sotpotatis/pomodoro-timer/pcb/production_files/rev 1.0.1/pcbway/sample_pcbway_order_information.png

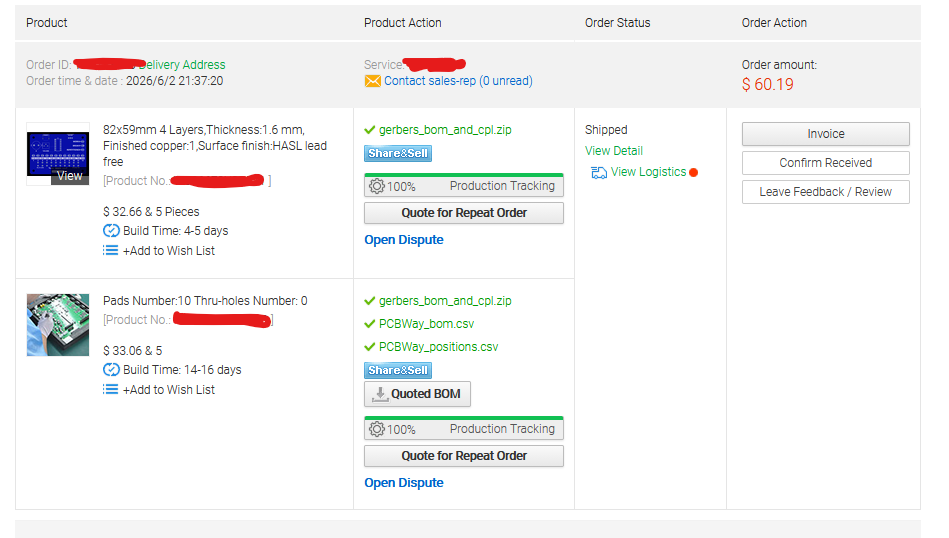
pcb/production_files/rev 1.0.1/pcbway/sample_pcbway_order_information.png
