sotpotatis/pomodoro-timer/tests/charlieplexing_15_pins/charlieplexing_15_pins/charlieplexing_15_pins.ino

/* charlieplexing_15_leds.ino
Test Arduino sketch (to run on an Arduino UNO, not Attinys)
for testing 5 pin Charlieplexing, which I added in the middle of my project.
Lights up each Charlieplexing LED at a time with a short delay in between
*/
// All GPIO pins in use.
const char TOTAL_PINS = 5;
 const char gpioPins[TOTAL_PINS] = {
   7,
   6,
   5,
   4,
   3
 };
// Contains the pins to set to output HIGH and output LOW to lit each of the 12 LEDs
// Led i is represented by index i in this map, and is in the format {pin to set to low, pin to set to high}
// Other pins are input pins.
// My schematic pins are called JP1, JP2, JP3, JP4, correspodning to GPIO pin number 1, 2, 3 and 4.
const char allPinStates[15][2] = {
  {gpioPins[1], gpioPins[0]}, // LED1  -> JP2 LOW, JP1 HIGH
  {gpioPins[0], gpioPins[1]}, // LED2  -> JP1 LOW, JP2 HIGH
  {gpioPins[2], gpioPins[0]}, // LED3  -> JP3 LOW, JP1 HIGH
  {gpioPins[0], gpioPins[2]}, // LED4  -> JP1 LOW, JP3 HIGH
  {gpioPins[3], gpioPins[0]}, // LED5  -> JP4 LOW, JP1 HIGH
  {gpioPins[0], gpioPins[3]}, // LED6  -> JP1 LOW, JP4 HIGH
  {gpioPins[2], gpioPins[1]}, // LED7  -> JP3 LOW, JP2 HIGH
  {gpioPins[1], gpioPins[2]}, // LED8  -> JP2 LOW, JP3 HIGH
  {gpioPins[3], gpioPins[1]}, // LED9  -> JP4 LOW, JP2 HIGH
  {gpioPins[1], gpioPins[3]}, // LED10 -> JP2 LOW, JP4 HIGH
  {gpioPins[3], gpioPins[2]}, // LED11 -> JP4 LOW, JP3 HIGH
  {gpioPins[2], gpioPins[3]},  // LED12 -> JP3 LOW, JP4 HIGH
  {gpioPins[3], gpioPins[4]},  // LED13 -> JP4 LOW, JP5 HIGH
  {gpioPins[4], gpioPins[3]},  // LED14 -> JP5 LOW, JP4 HIGH
  {gpioPins[4], gpioPins[2]}  // LED15 -> JP5 LOW, JP3 HIGH
};

 // Set all pins to inputs. Used for clearing the LEDs.
 void setAllPinsToInputs(){
   for (int i=0;i<TOTAL_PINS;i++){
      pinMode(gpioPins[i], INPUT);
   }
 }
// Given a pointer to a 2-element char array in the format {pin to set to low, pin to set to high},
// sets one of the pins to low and the other one to high.
 void setPinState(const char* pinState){
   for (int i=0;i<2;i++){
     const char pin = *pinState;
     pinMode(pin, OUTPUT);
     digitalWrite(pin, i == 1);
     pinState++;
   }
 }
 void setup() {
   // Set up pins
   setAllPinsToInputs();
 }
 void loop() {
   for (int i = 0; i < 15; i++) {
     // For each pin state, set the LEDs accordingly
     setPinState(allPinStates[i]);
     delay(1);
     setAllPinsToInputs();
  }
 }
